nosknut/bachelor-thesis/src/twig_3d_models/twig/twig_housing_assembly.SLDASM

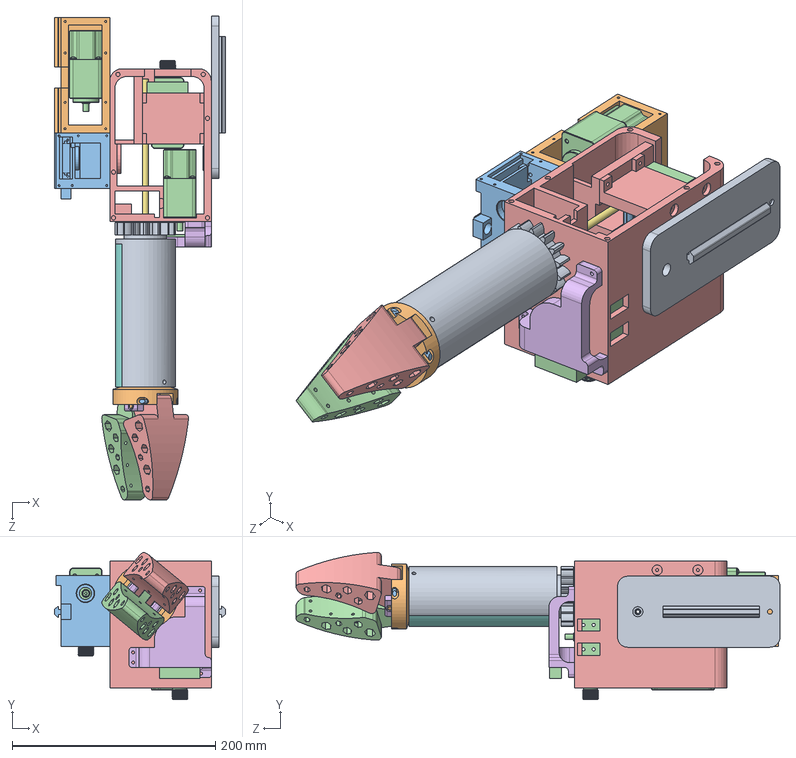
[picture p4: CAD file, 2024-05-20]
src/twig_3d_models/twig/twig_housing_assembly.SLDASM
168.7 x 144.9 x 476.6 mm
twig_housing
twig_servo bluetrail x 3
twig_housing_gripper_pinion
twig_arm_clamping_adapter_claw
twig_arm_47mm_bearing x 2
twig_arm_innerlockring
twig_arm_clamping_m6_rod
twig_arm_clamping_movable adapter
twig_arm_clamping_claw part_1
twig_arm_clamping_claw_part_2
twig_arm_clamping_rotating_pins x 2
twig_arm_clamping_pin4_movable_adapter
twig_arm_outer_shell_gear
twig_arm_outer_shell_lid
twig_arm_clamping_movable adapter_part2
twig_main_housing_encoder_wrist_mount_2
twig_main_housing_encoder_gripper_mount_2
twig_encoder_cartridge x 2
twig_side_mounts_right_gearbox_ny
twig_side_mounts_right_servo_housing
twig_side_mount_new
