nosknut/bachelor-thesis/src/twig_3d_models/twig/twig_arm_assembly.SLDASM

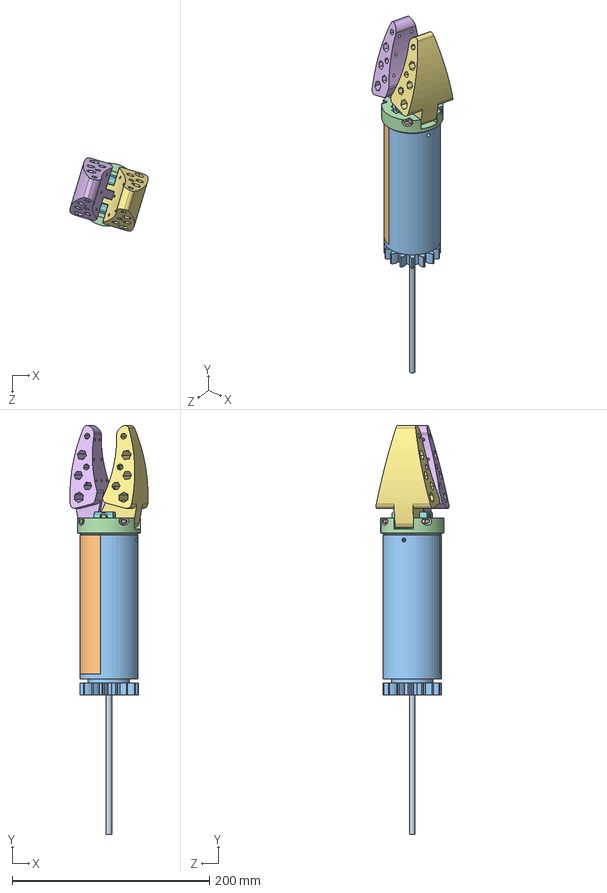
[picture p5: CAD file, 2024-05-20]
src/twig_3d_models/twig/twig_arm_assembly.SLDASM
79.0 x 414.6 x 74.1 mm
twig_arm_clamping_adapter_claw
twig_arm_47mm_bearing x 2
twig_arm_innerlockring
twig_arm_clamping_m6_rod
twig_arm_clamping_movable adapter
twig_arm_clamping_claw part_1
twig_arm_clamping_claw_part_2
twig_arm_clamping_rotating_pins x 2
twig_arm_clamping_pin4_movable_adapter
twig_arm_outer_shell_gear
twig_arm_outer_shell_lid
twig_arm_clamping_movable adapter_part2
