nosknut/bachelor-thesis/src/twig_3d_models/twig/twig_camera_adapter_1.SLDPRT

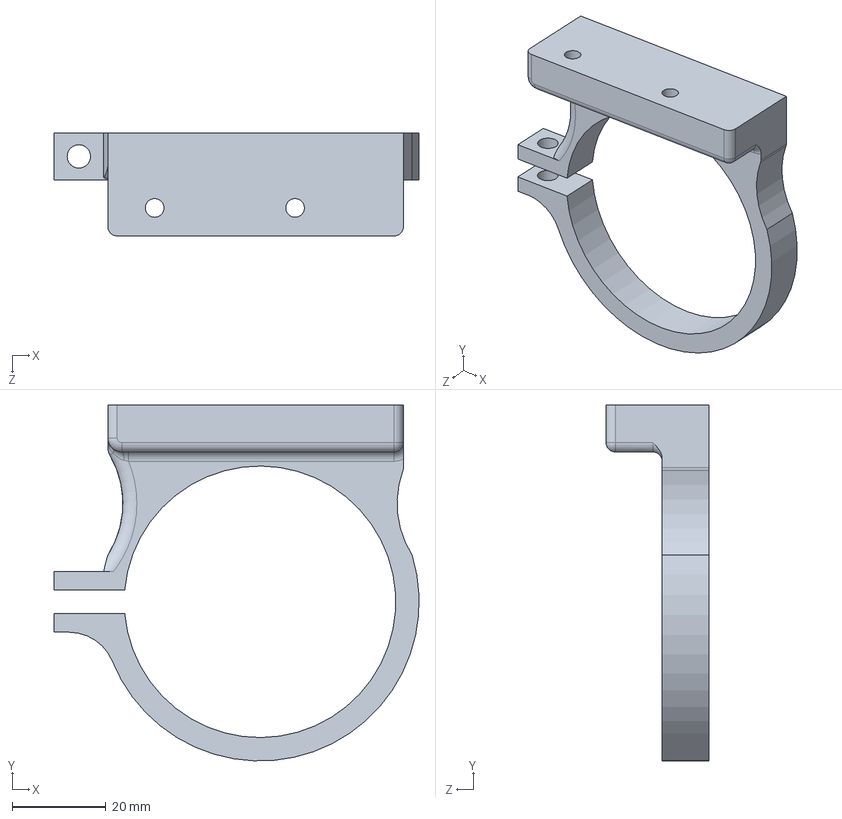
[picture p17: CAD file, 2024-05-20]
src/twig_3d_models/twig/twig_camera_adapter_1.SLDPRT
78.0 x 76.0 x 22.0 mm
