nosknut/bachelor-thesis/src/twig_3d_models/twig/twig_arm_clamping_movable adapter_part2.SLDPRT

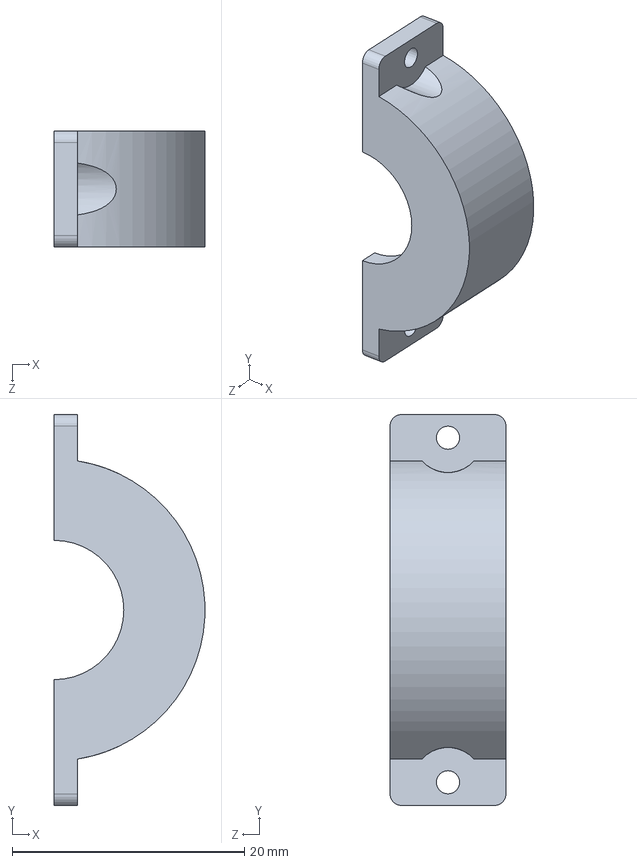
[picture p18: CAD file, 2024-05-20]
src/twig_3d_models/twig/twig_arm_clamping_movable adapter_part2.SLDPRT
13.0 x 33.7 x 10.0 mm
