nosknut/bachelor-thesis/src/twig_3d_models/twig/twig_arm_clamping_rotating_pins.SLDPRT

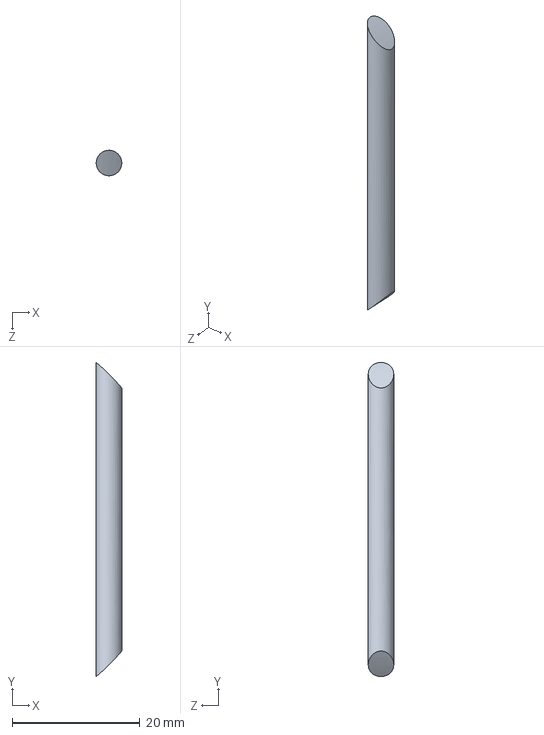
[picture p19: CAD file, 2024-05-20]
src/twig_3d_models/twig/twig_arm_clamping_rotating_pins.SLDPRT
4.00 x 49.1 x 4.00 mm
