nosknut/bachelor-thesis/src/twig_3d_models/twig/twig_side_mount_new.SLDPRT

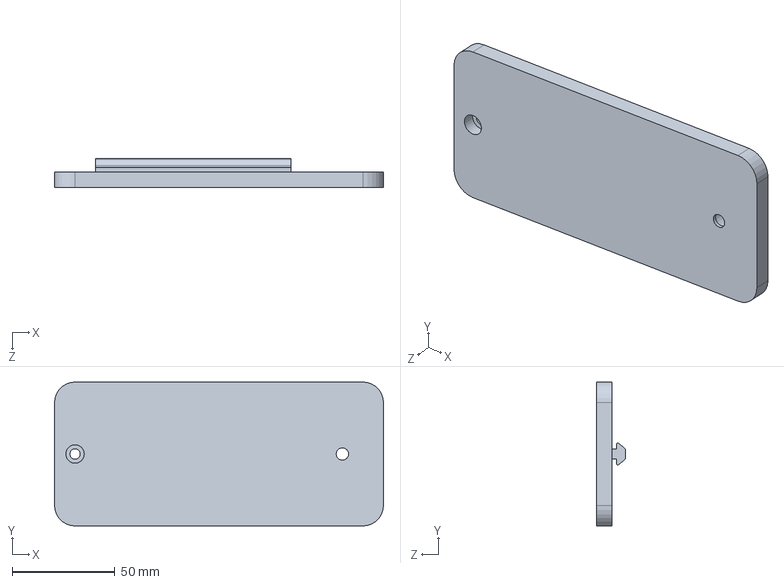
[picture p20: CAD file, 2024-05-20]
src/twig_3d_models/twig/twig_side_mount_new.SLDPRT
160.0 x 70.0 x 14.1 mm
