nosknut/bachelor-thesis/src/twig_3d_models/twig/twig_side_mounts_right_gearbox_ny.SLDPRT

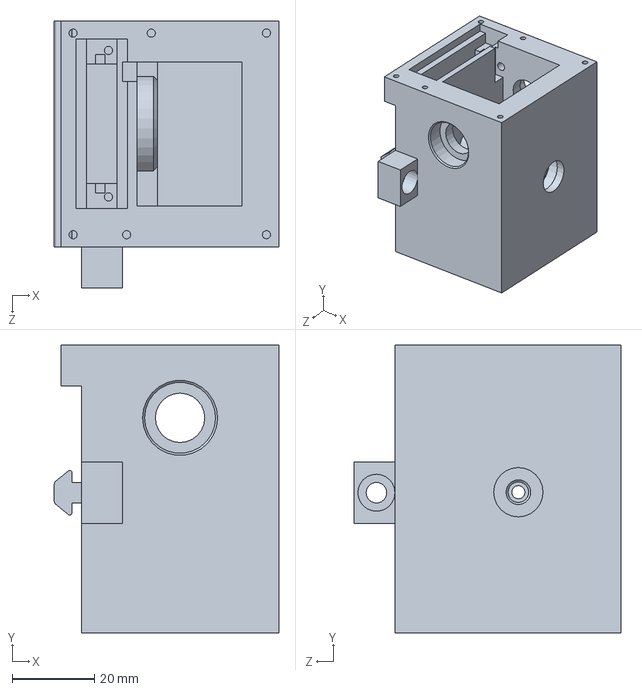
[picture p21: CAD file, 2024-05-20]
src/twig_3d_models/twig/twig_side_mounts_right_gearbox_ny.SLDPRT
54.6 x 70.0 x 65.0 mm
