nosknut/bachelor-thesis/src/twig_3d_models/twig/twig_arm_innerlockring.SLDPRT

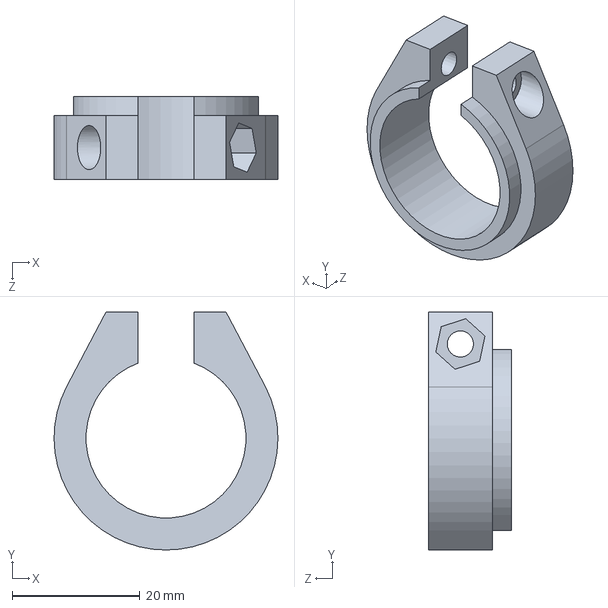
[picture p22: CAD file, 2024-05-20]
src/twig_3d_models/twig/twig_arm_innerlockring.SLDPRT
35.0 x 37.2 x 13.0 mm
