nosknut/bachelor-thesis/src/twig_3d_models/twig/twig_servo bluetrail.SLDPRT

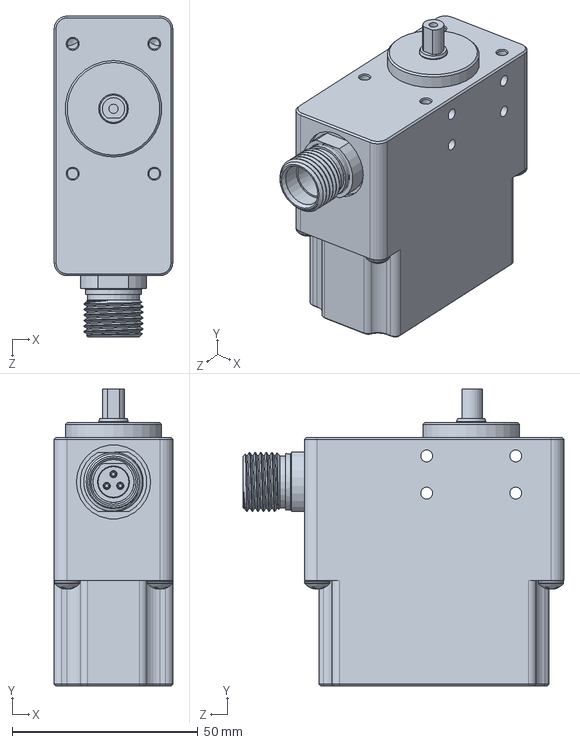
[picture p23: CAD file, 2024-05-20]
src/twig_3d_models/twig/twig_servo bluetrail.SLDPRT
32.0 x 80.0 x 86.5 mm
