nosknut/bachelor-thesis/src/twig_3d_models/twig/twig_arm_clamping_m6_rod.SLDPRT

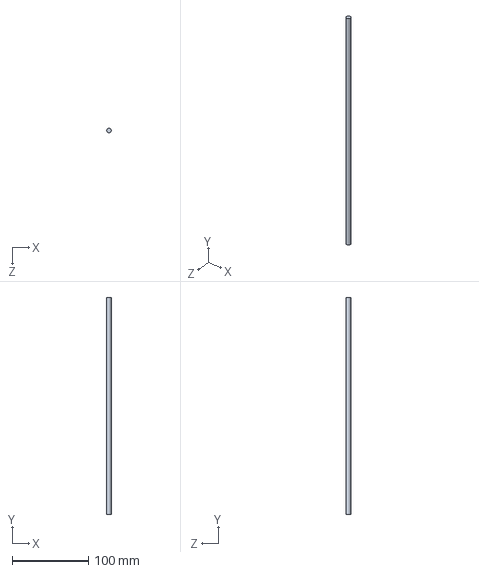
[picture p24: CAD file, 2024-05-20]
src/twig_3d_models/twig/twig_arm_clamping_m6_rod.SLDPRT
6.00 x 285.0 x 6.00 mm
