nosknut/bachelor-thesis/src/twig_3d_models/twig/twig_arm_clamping_claw part_1.SLDPRT

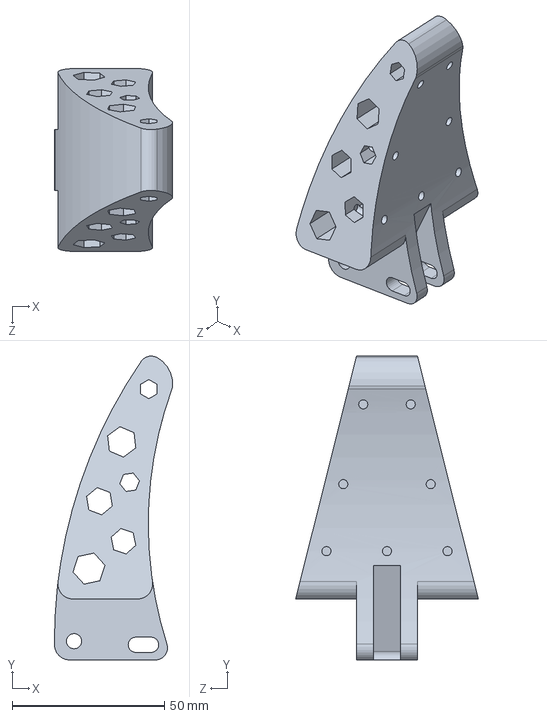
[picture p25: CAD file, 2024-05-20]
src/twig_3d_models/twig/twig_arm_clamping_claw part_1.SLDPRT
38.8 x 99.8 x 60.0 mm
