nosknut/bachelor-thesis/src/twig_3d_models/twig/twig_arm_clamping_adapter_claw.SLDPRT

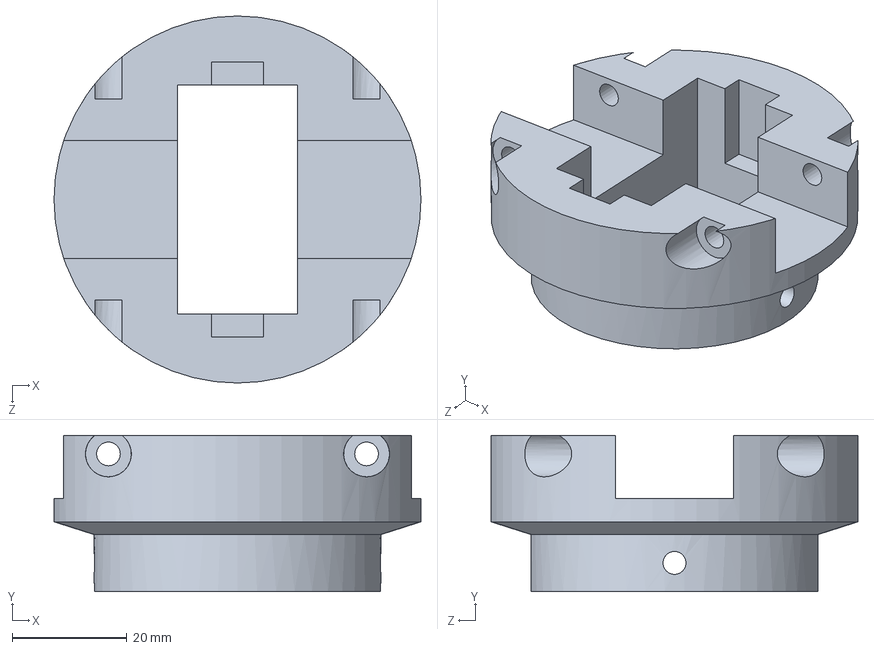
[picture p26: CAD file, 2024-05-20]
src/twig_3d_models/twig/twig_arm_clamping_adapter_claw.SLDPRT
64.0 x 27.2 x 64.0 mm
