nosknut/bachelor-thesis/src/twig_3d_models/twig/twig_housing_wrist_gear.SLDPRT

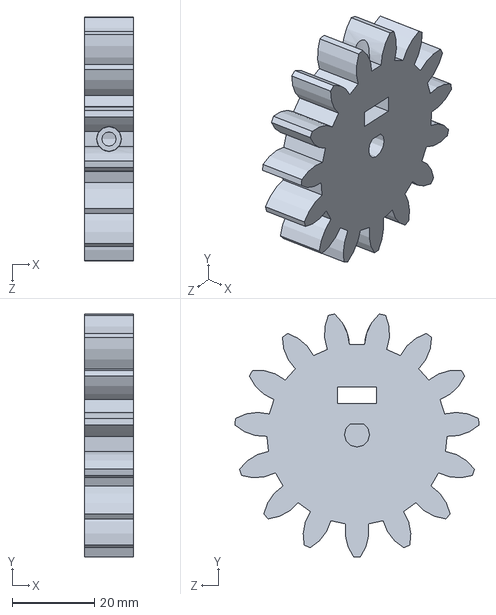
[picture p27: CAD file, 2024-05-20]
src/twig_3d_models/twig/twig_housing_wrist_gear.SLDPRT
12.0 x 59.0 x 59.3 mm
