nosknut/bachelor-thesis/src/twig_3d_models/twig/twig_arm_47mm_bearing.SLDPRT

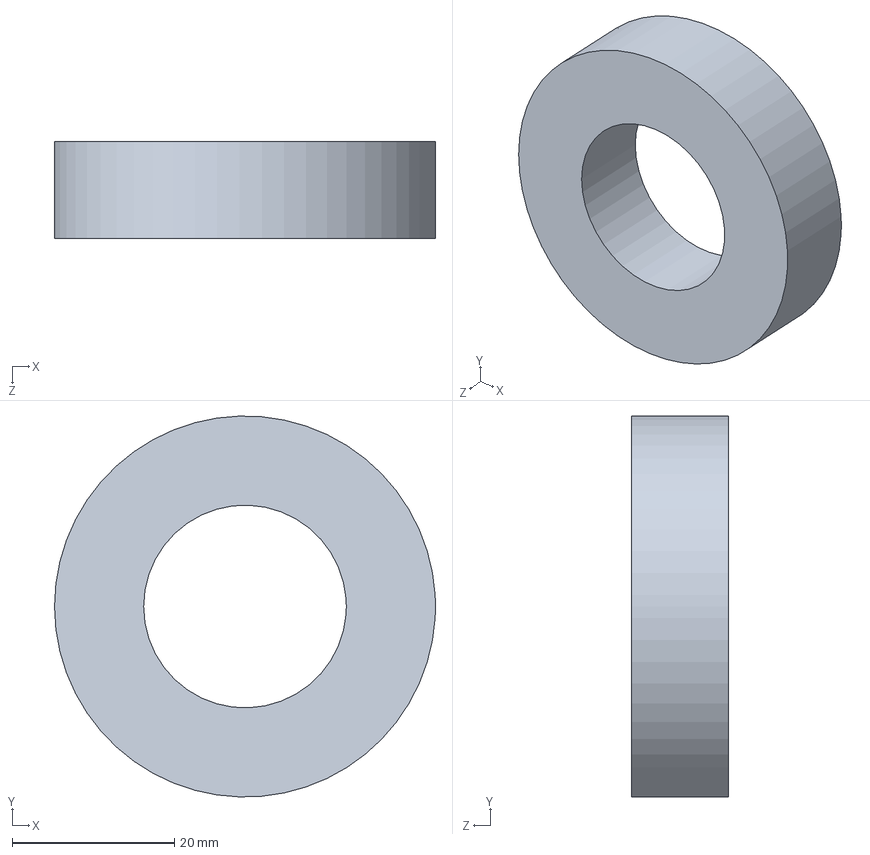
[picture p28: CAD file, 2024-05-20]
src/twig_3d_models/twig/twig_arm_47mm_bearing.SLDPRT
47.0 x 47.0 x 12.0 mm
