nosknut/bachelor-thesis/src/twig_hardware/include/twig_hardware/twig_hardware.hpp

// https://github.com/ros-controls/ros2_control_demos/blob/humble/example_12/hardware/include/ros2_control_demo_example_12/rrbot.hpp

// Copyright 2023 ros2_control Development Team
//
// Licensed under the Apache License, Version 2.0 (the "License");
// you may not use this file except in compliance with the License.
// You may obtain a copy of the License at
//
//     http://www.apache.org/licenses/LICENSE-2.0
//
// Unless required by applicable law or agreed to in writing, software
// distributed under the License is distributed on an "AS IS" BASIS,
// WITHOUT WARRANTIES OR CONDITIONS OF ANY KIND, either express or implied.
// See the License for the specific language governing permissions and
// limitations under the License.

#ifndef TWIG_HARDWARE_HPP_
#define TWIG_HARDWARE_HPP_

#include <memory>
#include <string>
#include <vector>

#include "hardware_interface/handle.hpp"
#include "hardware_interface/hardware_info.hpp"
#include "hardware_interface/system_interface.hpp"
#include "hardware_interface/types/hardware_interface_return_values.hpp"
#include "rclcpp/macros.hpp"
#include "rclcpp_lifecycle/node_interfaces/lifecycle_node_interface.hpp"
#include "rclcpp_lifecycle/state.hpp"
#include "twig_hardware/visibility_control.h"
#include "twig_hardware/twig_lib.hpp"

namespace twig_hardware
{
class TwigHardware : public hardware_interface::SystemInterface
{
public:
  RCLCPP_SHARED_PTR_DEFINITIONS(TwigHardware);

  TWIG_HARDWARE_PUBLIC
  hardware_interface::CallbackReturn on_init(
    const hardware_interface::HardwareInfo & info) override;

  TWIG_HARDWARE_PUBLIC
  hardware_interface::CallbackReturn on_configure(
    const rclcpp_lifecycle::State & previous_state) override;

  TWIG_HARDWARE_PUBLIC
  std::vector<hardware_interface::StateInterface> export_state_interfaces() override;

  TWIG_HARDWARE_PUBLIC
  std::vector<hardware_interface::CommandInterface> export_command_interfaces() override;

  TWIG_HARDWARE_PUBLIC
  hardware_interface::CallbackReturn on_activate(
    const rclcpp_lifecycle::State & previous_state) override;

  TWIG_HARDWARE_PUBLIC
  hardware_interface::CallbackReturn on_deactivate(
    const rclcpp_lifecycle::State & previous_state) override;

  TWIG_HARDWARE_PUBLIC
  hardware_interface::return_type read(
    const rclcpp::Time & time, const rclcpp::Duration & period) override;

  TWIG_HARDWARE_PUBLIC
  hardware_interface::return_type write(
    const rclcpp::Time & time, const rclcpp::Duration & period) override;

private:
  TwigLib twig;

  // Buffers read and modified by ros2_control
  std::vector<double> hw_commands_;
  std::vector<double> hw_states_;

  bool first_read_pass_ = true;
  bool first_write_pass_ = true;

  rclcpp::Time last_read_time_;
  rclcpp::Time last_write_time_;

  double pull_rate_;
  double push_rate_;
};

}  // namespace twig_hardware

#endif  // TWIG_HARDWARE_HPP_
