nosknut/bachelor-thesis/src/twig_teleop/config/joystick_direct_teleop.config.yaml

/twig_teleop_direct:
  ros__parameters:
    joy:
      axis:
        gripper: 3
        shoulder: 1
        wrist: 0
      button:
        activate_servos: 9
        deactivate_servos: 8
        deadmanswitch: 7
      deadband: 0.2
    shoulder_max_speed: 1.0
    wrist_max_speed: 1.0
    gripper_max_speed: 1.0
